dieleoz/balizas/1 Firmware/Doc Aplicativo Movil/Info Aplicativo Movil.docx

INFORMACION APLICATIVO MOVIL

1) Acceso al aplicativo
  a. Nombre: admin
  b. Contraseña: admin

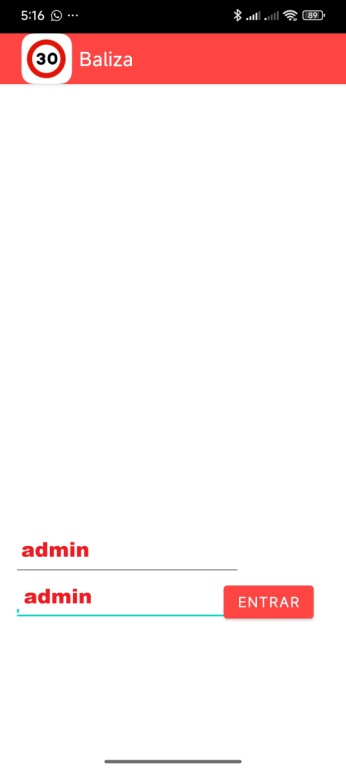
[picture p1: figure]

2) Configuración
  a. 1: Escanear bluetooth
  b. 2: Leer configuraciones Baliza
  c. 3: enviar la configuración a la Baliza
  d. 4: Selección de la alarma, máximo 5
  e. 5: Activar la alarma
  f. 6: Hora inicio alarma
  g. 7: Hora final alarma
  h. 8: activación de la alarma = diario, lunes a viernes, fin de semana

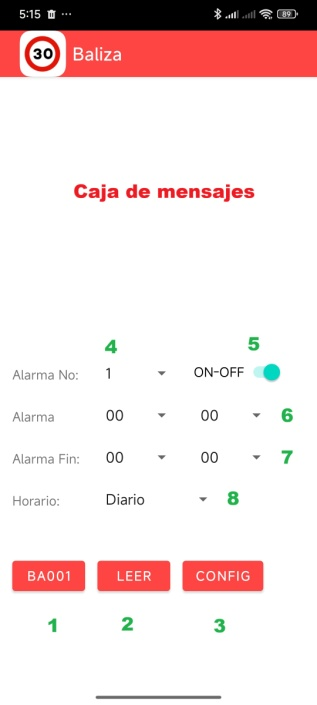
[picture p2: figure]
