dieleoz/balizas/3 Imagen/Horario.jpeg

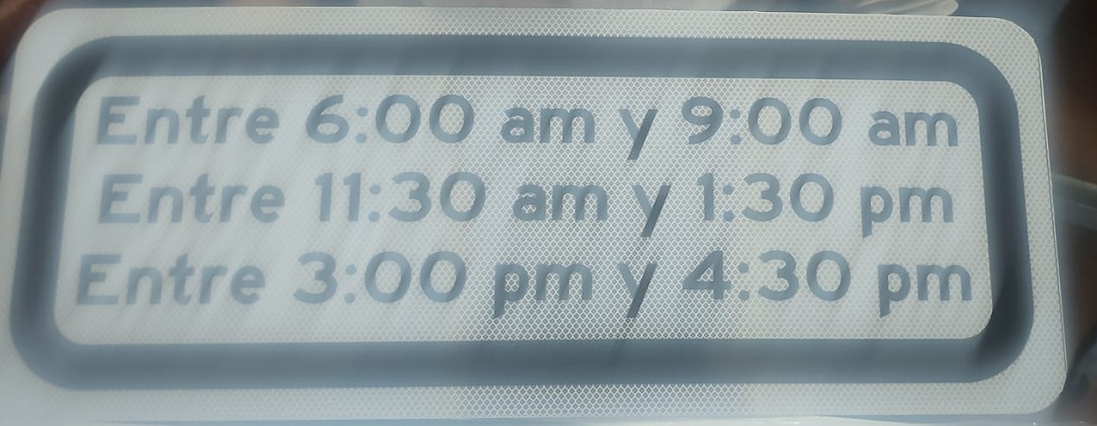
3 Imagen/Horario.jpeg
