dieleoz/balizas/3 Imagen/senal.jpeg

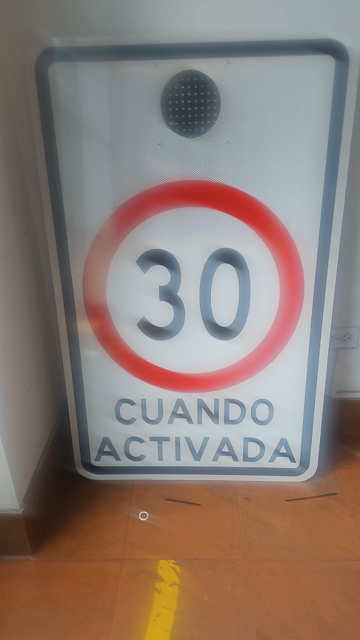
3 Imagen/senal.jpeg
