dieleoz/balizas/3 Imagen/WhatsApp Image 2026-08-21 at 4.49.41 PM.jpeg

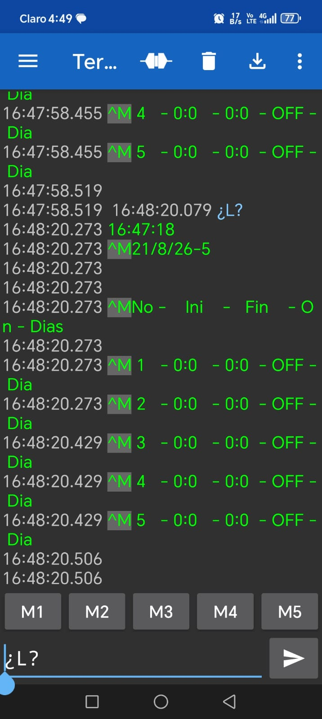
3 Imagen/WhatsApp Image 2026-08-21 at 4.49.41 PM.jpeg
