dieleoz/balizas/1 Firmware/Doc mplabx/18f2550_baliza_ V1.X/I2C.c

#include "I2C.h"
#include "main.h"

#include <xc.h>




void I2C_Master_Init(uint32_t clock)
{
    TRISBbits.RB0 = PIN_IN;    
    TRISBbits.RB1 = PIN_IN;
    
    SSPSTATbits.SMP = 1;       // Frecuencia de operacion Standard velocidad 100kHz-1Mhz
    SSPCON1bits.SSPEN = 1;     // habilito los pines para I2C
    SSPCON1bits.SSPM = 0b1000; // modo maestro i2c
    
    // FORMULA DE DATASHEET: CLOCK = Fosc/(4*(SSPADD+1)) 
    //despejamos SSPADD
    SSPADD = (uint8_t)((_XTAL_FREQ/(4.0*clock))-1);
    SSPCON2=0x00;             //clareo el registro que tiene las configuraciones del I2C    
}


void I2C_Master_Wait(void){
    uint16_t timeout = 5000;
    while( ((SSPCON2 & 0b00011111) || (SSPSTAT & 0b00000100)) && --timeout );
}

void I2C_Start(void){
    I2C_Master_Wait();
    SSPCON2bits.SEN = 1; //mando la condicion de start
}

void I2C_Stop(void){
    I2C_Master_Wait();
    SSPCON2bits.PEN = 1; //mando la condicion de stop
}

void I2C_Repeated_Start(void){
    I2C_Master_Wait();
    SSPCON2bits.RSEN = 1; //mando la condicion de repetir start   
}

void I2C_Master_Write(uint8_t dato){
    I2C_Master_Wait();
    SSPBUF = dato;      //cargamos el dato en el buffer para enviar
}

uint8_t I2C_Master_Read(uint8_t ACK){
    uint8_t dato;
    I2C_Master_Wait();
    SSPCON2bits.RCEN = 1; //habilito la recepcion de datos
    I2C_Master_Wait();
    dato = SSPBUF;         //leo el dato de SSPBUF
    I2C_Master_Wait();
    //el que MANDA el ACK es el que RECIBE el dato
    //el maestro esta mandando ACK
    //el ACK es para indicarle si el dato llego o no llego, como el maestro recibio el dato tiene que indicar como lo recibio
    SSPCON2bits.ACKDT = (ACK)?0:1; //bit de acknowledge //condicional?TRUE:FALSE; 
    //si a=1 -> ACKDT = 0 (Acknowledge)    RECONOCIMIENTO    - EL DATO LLEGO CON EXITO
    //si a=0 -> ACKDT = 1 (No Acknowledge) NO RECONOCIMIENTO - EL DATO LLEGO CON PROBLEMAS
    
    //Y AHORA RECIEN ENVIAMOS EL ACK CON ACKEN
    SSPCON2bits.ACKEN = 1; //transmite el bit de dato de ACKDT 
    return dato;   
}
