dieleoz/balizas/1 Firmware/Doc mplabx/18f2550_baliza_ V1.X/DS1307.h

#ifndef DS1307_H
#define	DS1307_H

#include <stdint.h>

typedef struct
{
    unsigned char seg;
    unsigned char min;
    unsigned char hor;
    
    unsigned char day;
    unsigned char month;
    unsigned char year;
     
    unsigned char dayWeek;
}strRtc;

enum Dias_semana
{
    LUNES = 1,
    MARTES,
    MIERCOLES,
    JUEVES,
    VIERNES,
    SABADO,
    DOMINGO
};

//*** PROTOTIPO DE LAS FUNCIONES ****
uint8_t BCD_a_Decimal(uint8_t numero); //Función que convierte un número BCD a decimal.
uint8_t Decimal_a_BCD(uint8_t numero); //Función que convierte un número decimal a BCD. 
void leerRtcSeg(uint8_t *segundos);
void leerRTC(uint8_t *hora, uint8_t *minutos, uint8_t *segundos, uint8_t *dia, uint8_t *mes, uint8_t *ano, uint8_t *diaSe);
void escribirRTC(uint8_t hor, uint8_t min, uint8_t seg, uint8_t dia, uint8_t mes, uint8_t ano, uint8_t diaSe);

#endif	/* DS1307_H */
