dieleoz/balizas/1 Firmware/Doc mplabx/18f2550_baliza_ V1.X/TimeBase.h

/* 
 * File:   TimeBase.h
 * Author: RentAdvisor
 *
 * Created on November 5, 2020, 8:39 AM
 */

#ifndef TIMEBASE_H
#define	TIMEBASE_H

#ifdef	__cplusplus
extern "C" {
#endif


//*** PROTOTIPO DE LAS FUNCIONES ***
unsigned long getMillis(void);
//unsigned long get100us(void);


#ifdef	__cplusplus
}
#endif

#endif	/* TIMEBASE_H */
