dieleoz/balizas/1 Firmware/Doc mplabx/18f2550_baliza_ V1.X/UART.h

/*
 * File:   UART.h
 */

void UART_init()
{
    TRISCbits.TRISC7 = 1;   //RX input
    TRISCbits.TRISC6 = 0;   //TX output 
    
    TXSTAbits.SYNC = 0;     //UART
    TXSTAbits.TX9 = 0;      //8 BITS
    TXSTAbits.BRGH = 1;     //ALTA VELOCIDAD
    SPBRG = 129;            //9600 a 20MHZ
    RCSTAbits.SPEN = 1;     //UART on    
    TXSTAbits.TXEN = 1;    //TX on
    RCSTAbits.CREN = 1;     //RX on
}

void UART_init_baud(const long int baudRate)
{
     

    
    
    TXSTAbits.BRGH = 0;
    
    TRISCbits.TRISC7 = 1;   //RX input
    TRISCbits.TRISC6 = 0;   //TX output 
    
    TXSTAbits.SYNC = 0;     //UART
    TXSTAbits.TX9 = 0;      //8 BITS
   
    SPBRG = 32;
    //SPBRG = valor;            //9600 a 20MHZ
    RCSTAbits.SPEN = 1;     //UART on    
    TXSTAbits.TXEN = 1;    //TX on
    RCSTAbits.CREN = 1;     //RX on
    
    
    PIE1bits.RCIE = 1;      //enable interrupt rx
}

char UART_read(void)
{
    if (PIR1bits.RCIF == 1)
    {
        
        
        if(RCSTAbits.OERR)
        {
            RCSTAbits.CREN = 0;
            NOP();
            RCSTAbits.CREN = 1;          
        }
        return RCREG;
    }
        
    else
        return 0;
}

void UART_write(char dato)
{
    TXREG = dato;
     while(TXSTAbits.TRMT == 0);
}

void UART_printf(unsigned char *cadena)
{
    while(*cadena !=0x00)
    {
        UART_write(*cadena);
        cadena++;
    }
}

void putch(char dato)
{
    UART_write(dato);
}
